anmaped/opaq/data/binaries/screenshots/dimmer.png

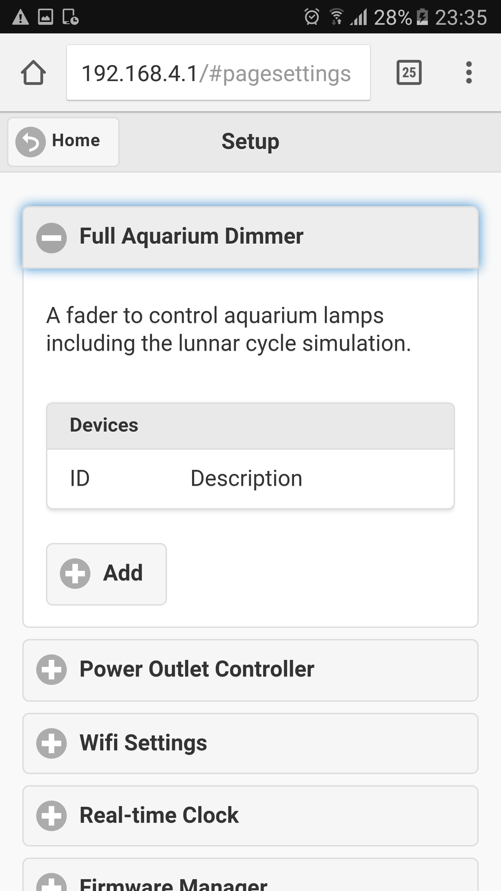
data/binaries/screenshots/dimmer.png
