anmaped/opaq/gfx.cpp

#include "gfx.h"

unsigned long testFillScreen() {
  unsigned long start = micros();
  tft.fillScreen(ILI9341_BLACK);
  tft.fillScreen(ILI9341_RED);
  tft.fillScreen(ILI9341_GREEN);
  tft.fillScreen(ILI9341_BLUE);
  tft.fillScreen(ILI9341_BLACK);
  return micros() - start;
}

unsigned long testText() {
  tft.fillScreen(ILI9341_BLACK);
  unsigned long start = micros();
  tft.setCursor(0, 0);
  tft.setTextColor(ILI9341_WHITE);
  tft.setTextSize(1);
  tft.println("Hello World!");
  tft.setTextColor(ILI9341_YELLOW);
  tft.setTextSize(2);
  tft.println(1234.56);
  tft.setTextColor(ILI9341_RED);
  tft.setTextSize(3);
  tft.println(0xDEADBEEF, HEX);
  tft.println();
  tft.setTextColor(ILI9341_GREEN);
  tft.setTextSize(5);
  tft.println("Groop");
  tft.setTextSize(2);
  tft.println("I implore thee,");
  tft.setTextSize(1);
  tft.println("my foonting turlingdromes.");
  tft.println("And hooptiously drangle me");
  tft.println("with crinkly bindlewurdles,");
  tft.println("Or I will rend thee");
  tft.println("in the gobberwarts");
  tft.println("with my blurglecruncheon,");
  tft.println("see if I don't!");
  return micros() - start;
}

unsigned long testLines(uint16_t color) {
  unsigned long start, t;
  int x1, y1, x2, y2, w = tft.width(), h = tft.height();

  tft.fillScreen(ILI9341_BLACK);
  delay(0);

  x1 = y1 = 0;
  y2 = h - 1;
  start = micros();
  for (x2 = 0; x2 < w; x2 += 6)
    tft.drawLine(x1, y1, x2, y2, color);
  x2 = w - 1;
  for (y2 = 0; y2 < h; y2 += 6)
    tft.drawLine(x1, y1, x2, y2, color);
  t = micros() - start; // fillScreen doesn't count against timing

  tft.fillScreen(ILI9341_BLACK);
  delay(0);

  x1 = w - 1;
  y1 = 0;
  y2 = h - 1;
  start = micros();
  for (x2 = 0; x2 < w; x2 += 6)
    tft.drawLine(x1, y1, x2, y2, color);
  x2 = 0;
  for (y2 = 0; y2 < h; y2 += 6)
    tft.drawLine(x1, y1, x2, y2, color);
  t += micros() - start;

  tft.fillScreen(ILI9341_BLACK);
  delay(0);

  x1 = 0;
  y1 = h - 1;
  y2 = 0;
  start = micros();
  for (x2 = 0; x2 < w; x2 += 6)
    tft.drawLine(x1, y1, x2, y2, color);
  x2 = w - 1;
  for (y2 = 0; y2 < h; y2 += 6)
    tft.drawLine(x1, y1, x2, y2, color);
  t += micros() - start;

  tft.fillScreen(ILI9341_BLACK);
  delay(0);

  x1 = w - 1;
  y1 = h - 1;
  y2 = 0;
  start = micros();
  for (x2 = 0; x2 < w; x2 += 6)
    tft.drawLine(x1, y1, x2, y2, color);
  x2 = 0;
  for (y2 = 0; y2 < h; y2 += 6)
    tft.drawLine(x1, y1, x2, y2, color);

  return micros() - start;
}

unsigned long testFastLines(uint16_t color1, uint16_t color2) {
  unsigned long start;
  int x, y, w = tft.width(), h = tft.height();

  tft.fillScreen(ILI9341_BLACK);
  start = micros();
  for (y = 0; y < h; y += 5)
    tft.drawFastHLine(0, y, w, color1);
  for (x = 0; x < w; x += 5)
    tft.drawFastVLine(x, 0, h, color2);

  return micros() - start;
}

unsigned long testRects(uint16_t color) {
  unsigned long start;
  int n, i, i2, cx = tft.width() / 2, cy = tft.height() / 2;

  tft.fillScreen(ILI9341_BLACK);
  n = min(tft.width(), tft.height());
  start = micros();
  for (i = 2; i < n; i += 6) {
    i2 = i / 2;
    tft.drawRect(cx - i2, cy - i2, i, i, color);
  }

  return micros() - start;
}

unsigned long testFilledRects(uint16_t color1, uint16_t color2) {
  unsigned long start, t = 0;
  int n, i, i2, cx = tft.width() / 2 - 1, cy = tft.height() / 2 - 1;

  tft.fillScreen(ILI9341_BLACK);
  n = min(tft.width(), tft.height());
  for (i = n; i > 0; i -= 6) {
    delay(0);
    i2 = i / 2;
    start = micros();
    tft.fillRect(cx - i2, cy - i2, i, i, color1);
    t += micros() - start;
    // Outlines are not included in timing results
    tft.drawRect(cx - i2, cy - i2, i, i, color2);
  }

  return t;
}

unsigned long testFilledCircles(uint8_t radius, uint16_t color) {
  unsigned long start;
  int x, y, w = tft.width(), h = tft.height(), r2 = radius * 2;

  tft.fillScreen(ILI9341_BLACK);
  start = micros();
  for (x = radius; x < w; x += r2) {
    for (y = radius; y < h; y += r2) {
      tft.fillCircle(x, y, radius, color);
    }
  }

  return micros() - start;
}

unsigned long testCircles(uint8_t radius, uint16_t color) {
  unsigned long start;
  int x, y, r2 = radius * 2, w = tft.width() + radius,
            h = tft.height() + radius;

  // Screen is not cleared for this one -- this is
  // intentional and does not affect the reported time.
  start = micros();
  for (x = 0; x < w; x += r2) {
    for (y = 0; y < h; y += r2) {
      tft.drawCircle(x, y, radius, color);
    }
  }

  return micros() - start;
}

unsigned long testTriangles() {
  unsigned long start;
  int n, i, cx = tft.width() / 2 - 1, cy = tft.height() / 2 - 1;

  tft.fillScreen(ILI9341_BLACK);
  n = min(cx, cy);
  start = micros();
  for (i = 0; i < n; i += 5) {
    tft.drawTriangle(cx, cy - i,     // peak
                     cx - i, cy + i, // bottom left
                     cx + i, cy + i, // bottom right
                     tft.color565(0, 0, i));
  }

  return micros() - start;
}

unsigned long testFilledTriangles() {
  unsigned long start, t = 0;
  int i, cx = tft.width() / 2 - 1, cy = tft.height() / 2 - 1;

  tft.fillScreen(ILI9341_BLACK);
  start = micros();
  for (i = min(cx, cy); i > 10; i -= 5) {
    start = micros();
    tft.fillTriangle(cx, cy - i, cx - i, cy + i, cx + i, cy + i,
                     tft.color565(0, i, i));
    t += micros() - start;
    tft.drawTriangle(cx, cy - i, cx - i, cy + i, cx + i, cy + i,
                     tft.color565(i, i, 0));
  }

  return t;
}

unsigned long testRoundRects() {
  unsigned long start;
  int w, i, i2, cx = tft.width() / 2 - 1, cy = tft.height() / 2 - 1;

  tft.fillScreen(ILI9341_BLACK);
  w = min(tft.width(), tft.height());
  start = micros();
  for (i = 0; i < w; i += 6) {
    i2 = i / 2;
    tft.drawRoundRect(cx - i2, cy - i2, i, i, i / 8, tft.color565(i, 0, 0));
    delay(0);
  }

  return micros() - start;
}

unsigned long testFilledRoundRects() {
  unsigned long start;
  int i, i2, cx = tft.width() / 2 - 1, cy = tft.height() / 2 - 1;

  tft.fillScreen(ILI9341_BLACK);
  start = micros();
  for (i = min(tft.width(), tft.height()); i > 20; i -= 6) {
    i2 = i / 2;
    tft.fillRoundRect(cx - i2, cy - i2, i, i, i / 8, tft.color565(0, i, 0));
    delay(0);
  }

  return micros() - start;
}

LCD_HAL_Interface::LCD_HAL_Interface(Adafruit_ILI9341 &t) : tft(t) {}

void LCD_HAL_Interface::fillScreen(int a) const { tft.fillScreen(a); }

void LCD_HAL_Interface::drawText(int x, int y, const char *c, int d, int e,
                                 int f) const {
  tft.setCursor(x, y);
  tft.setTextColor(d);
  tft.setTextSize(f);
  tft.println(c);
}

int LCD_HAL_Interface::getWidth() const { tft.getWidth(); }

int LCD_HAL_Interface::getHeight() const { tft.getHeight(); }

void LCD_HAL_Interface::drawCircle(int x, int y, int s, int color) const {
  tft.fillRect(x, y, s, s, color);
}

void LCD_HAL_Interface::fillCircle(int x, int y, int s, int color) const {
  tft.fillRect(x, y, s, s, color);
}
