anmaped/opaq/opaq.h

//#define DEBUG_ESP_OPAQCOMMAND
//#define DEBUG_ESP_OPAQSTORAGE
#define DEBUG_ESP_OPAQCOPROG
#define DEBUG_ESP_PORT Serial

#define OPAQ_C1_SCREEN

#define FF(x) String(F(x)).c_str()

#define OPAQ_URL_FIRMWARE_UPLOAD "cloud.opaqproject.org"
