anmaped/opaq/avr/coprocessor/Rf433ook.cpp

/*
 *  Opaq is an Open AQuarium Controller firmware. It has been developed for
 *  supporting several aquarium devices such as ligh dimmers, power management
 *  outlets, water sensors, and peristaltic pumps. The main purpose is to
 *  control fresh and salt water aquariums.
 *
 *    Copyright (c) 2015 Andre Pedro. All rights reserved.
 *
 *  This file is part of opaq firmware for aquarium controllers.
 *
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
 */

#include "Rf433ook.h"
#include "digitalWriteFast.h"

#include<stdbool.h>
#include<Arduino.h>

#define PREPROCESS(a) !a

Rf433ook::Rf433ook()
{
  
}

void Rf433ook::set_pin(int pinout)
{
  // configure pin
  pinMode(pinout,OUTPUT);
  digitalWriteFast(pinout, HIGH);
  
  pin = pinout;
}

void Rf433ook::set_encoding(int device)
{
  encoding=device;
}

void Rf433ook::sendOOK(bool b)
{
  // EasyHome case
  if (encoding == CHANON_DIO_DEVICE)
  {
    if (b) {
        digitalWriteFast(pin, PREPROCESS(HIGH));
        delayMicroseconds(310);   //275 originally, but tweaked was 295.
        digitalWriteFast(pin, PREPROCESS(LOW));
        delayMicroseconds(1340);  //1225 originally, but tweakedwas 1203.
      } else {
        digitalWriteFast(pin, PREPROCESS(HIGH));
        delayMicroseconds(310);   //275 originally, but tweaked was 295.
        digitalWriteFast(pin, PREPROCESS(LOW));
        delayMicroseconds(310);   //275 originally, but tweaked was 295.
      }
    }
    
    // other cases...
}

void Rf433ook::sendBit(bool data_bit) {
  
  // EasyHome case
  if (encoding == CHANON_DIO_DEVICE)
  {
    // case encoding is manchester
    // Manchester bit 0 is PREPROCESS(HIGH) for 275uS and PREPROCESS(LOW) for 275uS
    // Manchester bit 1 is PREPROCESS(HIGH) for 275uS and PREPROCESS(LOW) for 1225uS
    // data bit 0 = Manchester encoding '01'
    // data bit 1 = Manchester encoding '10'
    // data bit 0 = PREPROCESS(HIGH) 275uS, PREPROCESS(LOW) 275uS, PREPROCESS(HIGH) 275uS, PREPROCESS(LOW) 1225uS
    // data bit 1 = PREPROCESS(HIGH) 275uS, PREPROCESS(LOW) 1225uS, PREPROCESS(HIGH) 275uS, PREPROCESS(LOW) 275uS
    
    if (data_bit) {
      sendOOK(true);
      sendOOK(false);
    } else {
      sendOOK(false);
      sendOOK(true);
    }
  }

  // other cases...
  
}

void Rf433ook::sendMessage(bool bit_vector[]) {
  
  // EasyHome case
  if (encoding == CHANON_DIO_DEVICE)
  {
    // preamble is PREPROCESS(HIGH) 275uS, PREPROCESS(LOW) 2675uS
    /*digitalWriteFast(pin, PREPROCESS(HIGH));
    delayMicroseconds(275);
    digitalWriteFast(pin, PREPROCESS(LOW));
    delayMicroseconds(2675);*/

    digitalWriteFast(pin, PREPROCESS(HIGH));
    delayMicroseconds(275);
    digitalWriteFast(pin, PREPROCESS(LOW));
    delayMicroseconds(9900);      // first lock
    digitalWriteFast(pin, PREPROCESS(HIGH));  // PREPROCESS(HIGH) again
    delayMicroseconds(275);       // wait
    digitalWriteFast(pin, PREPROCESS(LOW));   // second lock
    delayMicroseconds(2675);
    digitalWriteFast(pin, PREPROCESS(HIGH));
    
    // transmitter ID
    for (int i = 0; i < 26; i++) {
      sendBit(bit_vector[i]);
    }
    
    // bit 26 is the Group Flag,
    sendBit(bit_vector[26]);
    
    // bit 27 is the ON / OFF Flag
    sendBit(bit_vector[27]);
 
    // bits 28 - 31, are the Group Code (up to 16 units can be in the same group) 
    for (int i = 28; i < 32; i++) {
        sendBit(bit_vector[i]);
    }
    
    // bits 32 - 35 are the dim level (16 Levels)
    // unavailable for power socket outlets
    
    digitalWriteFast(pin, PREPROCESS(HIGH));   // lock - end of data
    delayMicroseconds(275);    // wait
    digitalWriteFast(pin, PREPROCESS(LOW));    // lock - end of signal
  }
  
  // other messages...
}

Rf433ook Rf433_transmitter;
